nektarios25ma/FACE-RECOGNITION-/photo απο lab STEM-VAMOS-2020-21/P10219-145822.jpg

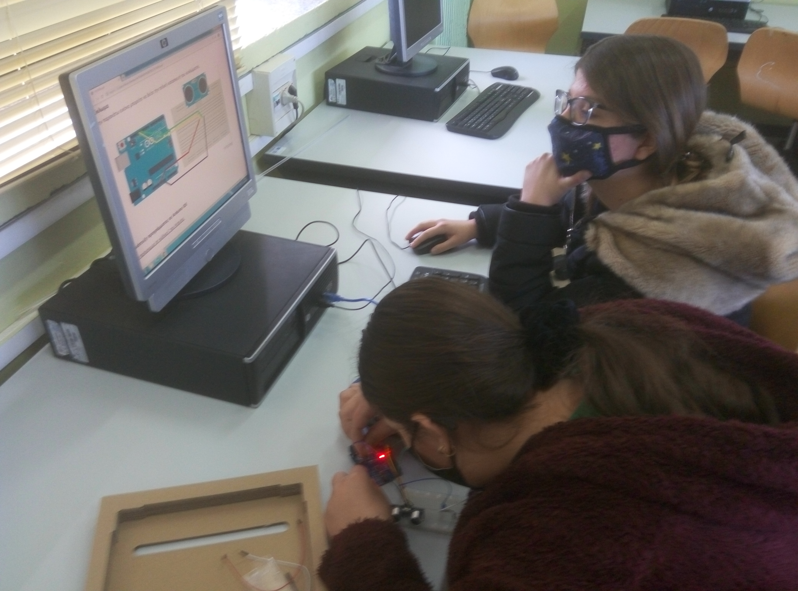
photo απο lab STEM-VAMOS-2020-21/P10219-145822.jpg
