nektarios25ma/FACE-RECOGNITION-/photo απο lab STEM-VAMOS-2020-21/P10226-144952.jpg

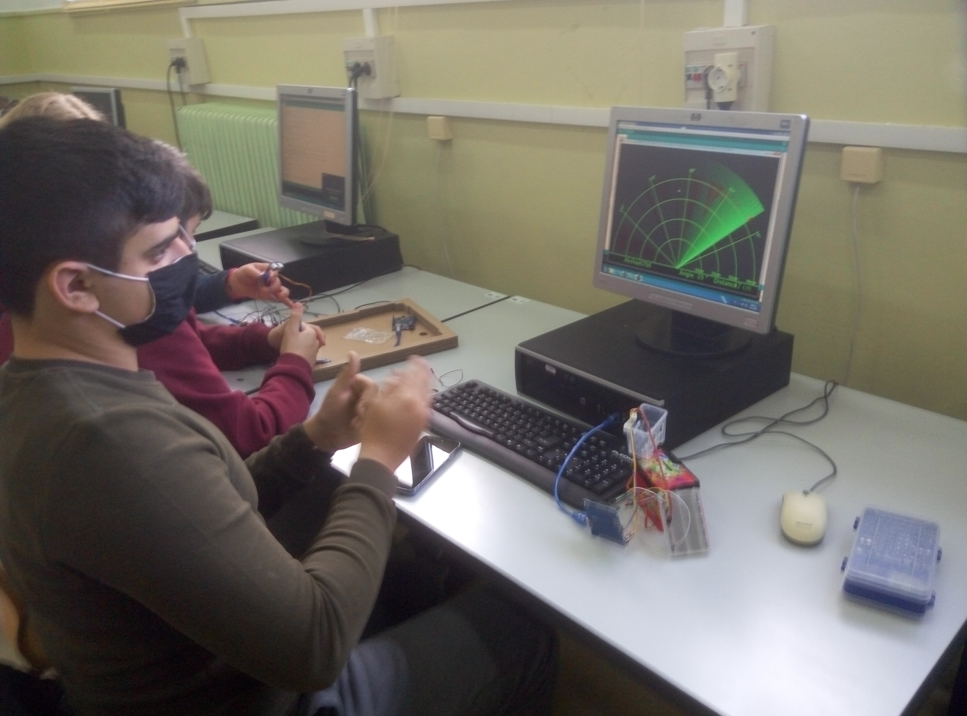
photo απο lab STEM-VAMOS-2020-21/P10226-144952.jpg
